SYSC4907-24/Pediatric-Laparoscopic-Surgery-Simulator/Hardware/CAD/screen-setup/Washer Locking v1.stl

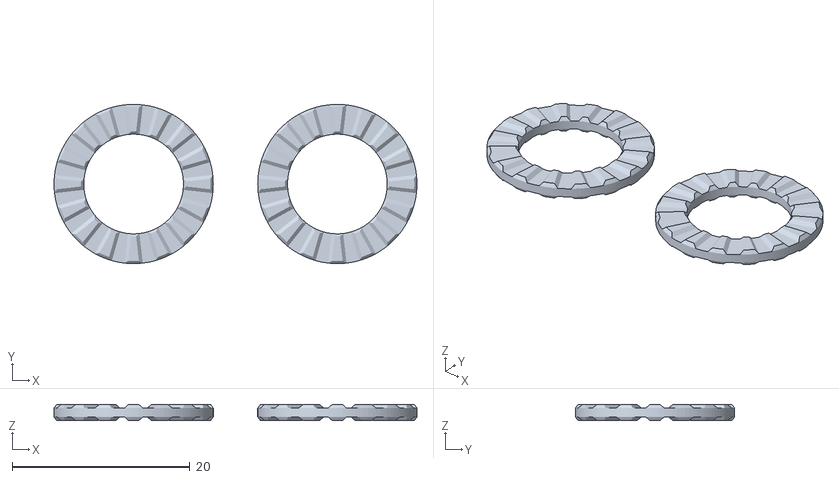
[picture p64: CAD file, 2024-04-23]
Hardware/CAD/screen-setup/Washer Locking v1.stl
40.8 x 17.9 x 1.80
