SYSC4907-24/Pediatric-Laparoscopic-Surgery-Simulator/Hardware/CAD/screen-setup/TClamp L Bolt.stl

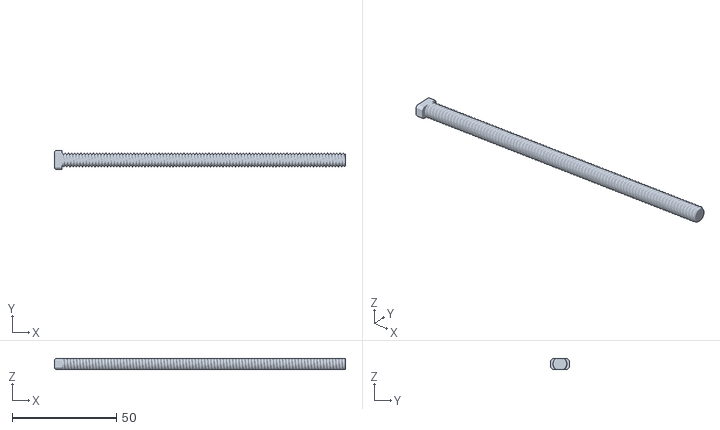
[picture p65: CAD file, 2024-04-23]
Hardware/CAD/screen-setup/TClamp L Bolt.stl
139.8 x 9.00 x 5.41
