SYSC4907-24/Pediatric-Laparoscopic-Surgery-Simulator/Hardware/CAD/screen-setup/Clamp Bolt v2.stl

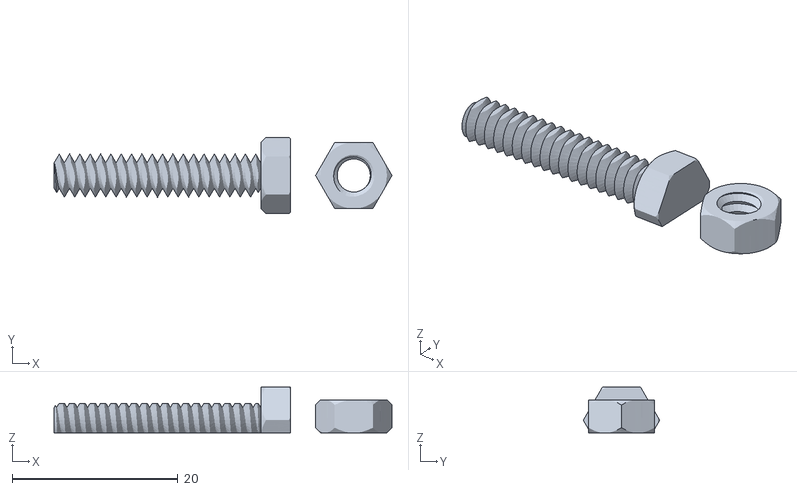
[picture p66: CAD file, 2024-04-23]
Hardware/CAD/screen-setup/Clamp Bolt v2.stl
40.8 x 9.24 x 5.53
